micro-nova/Mercury-CTDSP/LTspice3bitstage/CTDSP_v7.asc

C1: cap; 100nF
C2: cap; 100nF
C3: cap; 100nF
C4: cap; 1µF
C5: cap; 1µF
C6: cap; 1µF
R1: res; 1k
R2: res; 1k
R3: res; 1k
R4: res; 1k
U1: ADA4891
U2: ADA4891
U3: ADA4891
V1: voltage; 5
V2: voltage; SINE(2.5 2 5k)
X1: stage_1bit
X2: stage_1bit
X3: stage_1bit
X4: stage_1bit
Named nets: 0, VDD, VSS, Input, Tap0, S1, B1, Tap1, Tap2, B2, S2, B3, B4, S3, B5, B6, S4, B7, B8, Tap2_l, Tap0_l, Tap1_l
.tran 0 2m 0 1u uic
B1 quant 0 V=floor(V(Input)/0.0195)*0.0195
B_b1 b1_out 0 V=if(V(B1)>V(Tap1), 1, 0)
B_b2 b2_out 0 V=if(V(B2)>V(Tap1), 1, 0)
B_b3 b3_out 0 V=if(V(B3)>V(Tap1), 1, 0)
B_b4 b4_out 0 V=if(V(B4)>V(Tap1), 1, 0)
B_b5 b5_out 0 V=if(V(B5)>V(Tap1), 1, 0)
B_b6 b6_out 0 V=if(V(B6)>V(Tap1), 1, 0)
B_b7 b7_out 0 V=if(V(B7)>V(Tap1), 1, 0)
B_b8 b8_out 0 V=if(V(B8)>V(Tap1), 1, 0)
 
B2 reconstruction 0 V=((128*V(b1_out) + 64*V(b2_out) + 32*V(b3_out) + 16*V(b4_out) + 8*V(b5_out) + 4*V(b6_out) + 2*V(b7_out) + 1*V(b8_out))/255) * 5
.ic V(tap0_l)=1.25 V(tap1_l)=2.5 V(tap2_l)=3.75
