micro-nova/Mercury-CTDSP/LTspice3bitstage/Draft2.asc

C1: cap; 0.01µF
C2: cap; 0.1µF
R1: res; 1k
U1: NE555
V1: voltage; 5v
V2: voltage; PULSE(5 0 10ns 10ns 100us 100ns 5ms 2)
Named nets: 0, VCC, Pulse, out
.tran 0 20ms 0 20us
