micro-nova/Mercury-CTDSP/LTspice3bitstage/simple_stage.asc

C2: cap; 1n
R1: res; 10k
R2: res; 10k
R7: res; 10k
R8: res; 10k
R9: res; 10k
R10: res; 10k
R11: res; 1.4k
U1: LT1016
U4: LT1678
U5: LT1016
U6: ADG709
U7: LT1492
V1: voltage; 3.33
V2: voltage; 1.66
Named nets: VSS, DIFF, Out, VDD, Trig1, Trig2, Sig, 0, Tap1_sim, Tap2_sim, Tap1, Tap2
Simple RC filtering to smooth behavior of signal
when Tap is added/subtracted from it.
Simple switch that yields Tap when
Sig > Tap and GND when Sig < Tap.
Re-amplify signal to GND-5V for next stage.
Trig is when a level crossing occurs. Either a
rising or faslling edge indicates a level crossing.
Subtractor: Sig will always be
"constrained" from GND to 2.5V
