micro-nova/Mercury-CTDSP/LTspice3bitstage/stage_1bit.asc

C1: cap; 1pF
Encoder: Encoder
R1: res; 5k
R2: res; 5k
R3: res; 20k
R4: res; 20k
R5: res; 1k
R6: res; 1k
R7: res; 470k
R8: res; 470k
R9: res; 1k
R10: res; 470k
U1: ADG709
U2: ADA4891
U3: LTC6752
U4: LTC6752
U5: LTC6752
Named nets: VDD, Comp0, Tap0, Sig, Out, VSS, Comp1, Tap1, Comp2, Tap2, B1, B2
